thenetworkinglab/difnif/verilog/difnif_top.v

// DifNif
//
// Copyright (c) 2021 Eric Schlaepfer
// This work is licensed under CERN-OHL-S-2.0.
//
`default_nettype none
module difnif_top(
    // Clocks
    input clk_10m,

    // Unknown, FIXME better name
    input chreset_l,

    // Bus reset
    input chreset,

    // Micro Channel bus
    input cmd_l,        // Command clock
    input s0_w_l,       // S0 aka write#
    input s1_r_l,       // S1 aka read#
    input m_io_l,       // memory / IO# transfer
    input cd_setup_l,   // Card setup mode
    input addr_sel_in_l,// Card address selected
    input [15:0] bus_a, // Address bus (register select)
    input fulladdr_l,   // When high, only use 4 bits of address
    input sbhe_l,       // With bus_a0, selects 8 or 16 bit transfer
    output cd_ds16_l,   // Assert low to request 16-bit transfer
    output cd_chrdy_l,  // Channel ready (inserts wait states)
    output cd_sfdbk_l,  // Card selected feedback (72-pin only)

    inout[15:0]bus_d,   // Bidirectional data bus
    output data_dir,    // Data bus buffer direction control

    output irq14_l,     // Interrupt line

    input arb_gnt_l,    // DMA arbitration/grant mode
    input tc_l,         // DMA terminate count
    input [3:0]arb,     // DMA arbitration bus inputs
    input burst_l,      // DMA burst request input
    input preempt_l,    // DMA preempt request input
    output [3:0]arb_o,  // DMA arbitration control line outputs
    output burst_o_l,   // DMA burst request output
    output preempt_o_l, // DMA preempt request output

    // SD card (temporarily used for testing)
    output sd_clk,
    output sd_cmd,
    output [3:0]sd_d,
    input sd_switch,

    // LEDs
    output led0,
    output led1,

    // Teensy
    input tn_rd,
    input tn_wr,
    input [3:0]tn_addr,
    inout [15:0]tn_d,
    output tn_int,
    output tn_clk,
    input tn30
    );

    reg[22:0] counter;
    wire pll_lock;
    wire clk;

    // Teensy registers and controls
    wire [7:0] t_atn;
    wire t_atn_full;
    wire t_atn_read;
    wire [7:0] t_isr_out;
    wire t_isr_full;
    wire t_isr_write;
    wire [15:0] t_cifr;
    wire t_cifr_full;
    wire t_cifr_read;
    wire [15:0] t_sifr_out;
    wire t_sifr_full;
    wire t_sifr_write;

    wire [15:0] t_dreg_out;
    wire [15:0] t_dreg_in;
    wire t_treq_set;
    wire t_treq;
    wire t_treq_16;

    wire t_hard_reset;
    wire t_cmd_in_progress;
    wire t_busy_clear;
    wire t_clear_all;

    wire [39:0] t_pos_regs;

    wire addr_sel_l;
    wire fulladdr2_l;

    // Use pullup on fulladdr_l signal.
    SB_IO #(
        .PIN_TYPE(6'b0000_01),
        .PULLUP(1'b1)
    ) fulladdr_pad (
        .PACKAGE_PIN(fulladdr_l),
        .D_IN_0(fulladdr2_l)
    );

    // Address decoder for 72-pin version: 3510-3517, or 3518-351F when
    // POS 2 bit 1 selects the alternate address. The ThinkPad's system board
    // decodes the address itself and supplies addr_sel_in_l.
    wire alt_addr = t_pos_regs[17];
    assign addr_sel_l = fulladdr2_l ? addr_sel_in_l : ~(bus_a[15:3] == {12'h351, alt_addr});
    wire [3:0] reg_sel = fulladdr2_l ? bus_a[3:0] : {1'b0, bus_a[2:0]};

    mcabus mca1 (
        .clk(clk),
        .chreset(chreset),
        .chreset_l(chreset_l),
        .cmd_l(cmd_l),
        .s0_w_l(s0_w_l),
        .s1_r_l(s1_r_l),
        .m_io_l(m_io_l),
        .cd_setup_l(cd_setup_l),
        .addr_sel_l(addr_sel_l),
        .bus_a(reg_sel),
        .sbhe_l(sbhe_l),
        .cd_ds16_l(cd_ds16_l),
        .cd_chrdy_l(cd_chrdy_l),
        .cd_sfdbk_l(cd_sfdbk_l),

        .bus_d(bus_d),
        .data_dir(data_dir),

        .irq14_l(irq14_l),

        .arb_gnt_l(arb_gnt_l),
        .tc_l(tc_l),
        .arb(arb),
        .burst_l(burst_l),
        .preempt_l(preempt_l),
        .arb_o(arb_o),
        .burst_o_l(burst_o_l),
        .preempt_o_l(preempt_o_l),
        .test1(sd_clk), // FIXME testing
        .test2(sd_cmd),
        .tbus(sd_d), // more testing

        // Teensy connections
        .t_atn(t_atn),
        .t_atn_full(t_atn_full),
        .t_atn_read(t_atn_read),
        .t_isr_out(t_isr_out),
        .t_isr_full(t_isr_full),
        .t_isr_write(t_isr_write),
        .t_cifr(t_cifr),
        .t_cifr_full(t_cifr_full),
        .t_cifr_read(t_cifr_read),
        .t_sifr_out(t_sifr_out),
        .t_sifr_full(t_sifr_full),
        .t_sifr_write(t_sifr_write),
        .t_hard_reset(t_hard_reset),
        .t_cmd_in_progress(t_cmd_in_progress),
        .t_busy_clear(t_busy_clear),
        .t_dreg_out(t_dreg_out),
        .t_dreg_in(t_dreg_in),
        .t_treq_set(t_treq_set),
        .t_treq(t_treq),
        .t_treq_16(t_treq_16),
        .t_clear_all(t_clear_all),

        .t_pos_regs(t_pos_regs)
    );

    teensy tn1 (
        .tn_rd(tn_rd),
        .tn_wr(tn_wr),
        .tn_addr(tn_addr),
        .tn_d(tn_d),
        .tn_int(tn_int),
        .clk(clk),
        .tn30(tn30),

        // Register interface
        .t_atn(t_atn),
        .t_atn_full(t_atn_full),
        .t_atn_read(t_atn_read),
        .t_isr_out(t_isr_out),
        .t_isr_full(t_isr_full),
        .t_isr_write(t_isr_write),
        .t_cifr(t_cifr),
        .t_cifr_full(t_cifr_full),
        .t_cifr_read(t_cifr_read),
        .t_sifr_out(t_sifr_out),
        .t_sifr_full(t_sifr_full),
        .t_sifr_write(t_sifr_write),
        .t_hard_reset(t_hard_reset),
        .t_cmd_in_progress(t_cmd_in_progress),
        .t_busy_clear(t_busy_clear),
        .t_dreg_out(t_dreg_out),
        .t_dreg_in(t_dreg_in),
        .t_treq_set(t_treq_set),
        .t_treq(t_treq),
        .t_treq_16(t_treq_16),
        .t_clear_all(t_clear_all),

        .t_pos_regs(t_pos_regs)
    );
    // 50MHz
    `ifdef SYNTHESIS
    SB_PLL40_PAD #(
        .FEEDBACK_PATH("SIMPLE"),
        .DIVR(0),
        .DIVF(79),
        .DIVQ(4),
        .FILTER_RANGE(1)
    ) icetest_pll (
        .LOCK(pll_lock),
        .RESETB(1'b1),
        .BYPASS(1'b0),
        .PACKAGEPIN(clk_10m),
        .PLLOUTGLOBAL(clk)
    );
    `else
    assign clk = clk_10m;
    `endif

    assign tn_clk = 1'b0; // No clock for now
    //assign tn_clk = clk; // Clock to Teensy in case I want to make a synchronous interface

//    assign led0 = counter[22];
    assign led0 = fulladdr2_l;
    assign led1 = counter[21];

    always @ (posedge clk)
    begin
        counter <= counter + 1;
    end

endmodule
