thenetworkinglab/difnif/verilog/teensy.v

// DifNif
//
// Copyright (c) 2021 Eric Schlaepfer
// This work is licensed under CERN-OHL-S-2.0.
//

`default_nettype none
module teensy(
    // External connections to Teensy
    input tn_rd,
    input tn_wr,
    input [3:0]tn_addr,
    inout [15:0]tn_d,
    output tn_int,
    input clk,
    input tn30,

    // Connections to MCA interface
    // ATN register
    input [7:0] t_atn,
    input t_atn_full,
    output t_atn_read,

    // ISR register
    output [7:0] t_isr_out,
    input t_isr_full,
    output t_isr_write,

    // CIFR register
    input [15:0] t_cifr,
    input t_cifr_full,
    output t_cifr_read,

    // SIFR register
    output [15:0] t_sifr_out,
    input t_sifr_full,
    output t_sifr_write,

    // Flags
    input t_hard_reset,
    output t_cmd_in_progress,
    output t_busy_clear,
    output t_clear_all,

    // Data register
    input [15:0] t_dreg_out,
    output [15:0] t_dreg_in,
    output t_treq_set,
    input t_treq,
    input t_treq_16,

    input [39:0] t_pos_regs
    );

    localparam REG_TEST = 4'd0;
    localparam REG_FLAGS = 4'd1;
    localparam REG_ATN = 4'd2;
    localparam REG_ISR = 4'd3;
    localparam REG_CIFR = 4'd4;
    localparam REG_SIFR = 4'd5;
    localparam REG_DREG = 4'd6;
    localparam REG_POS01 = 4'd7;
    localparam REG_POS23 = 4'd8;
    localparam REG_POS4 = 4'd9;

    reg [15:0] tn_d_out;

    wire [15:0] flags_out;
    reg [15:0] flags_in = 16'H0000;

    reg [15:0] testreg = 16'HABCD;

    reg [7:0] t_isr;
    reg [15:0] t_sifr;
    reg [15:0] t_dreg;

    assign t_isr_out = t_isr;
    assign t_sifr_out = t_sifr;
    assign t_dreg_in = t_dreg;

    // Interrupt output
    assign tn_int = t_atn_full; // TODO: make this more complex

    wire t_busy_bit;

    // Flag register
    assign flags_out = {5'h0, t_clear_all,
                        t_treq_16, t_treq,
                        1'b1, t_cmd_in_progress, // Clear busy is active low
                        1'b0, t_hard_reset,
                        t_sifr_full, t_cifr_full,
                        t_isr_full, t_atn_full};

    // These bits in the flag reg are r/w
    assign t_cmd_in_progress = flags_in[6];
    assign t_clear_all = flags_in[10]; // ATN, BUSY, CI FULL, ISR, SI FULL, TREQ, TREQ_16
    // Note: Does not clear CmdInProgress

    // Clears the busy flag when bit is written to a '0'
    assign t_busy_clear = tn_wr & (tn_addr == REG_FLAGS) & ~tn_d[7];

    // Sets the transfer request flag when bit is written to a '1'
    assign t_treq_set = tn_wr & (tn_addr == REG_FLAGS) & tn_d[5];

    // Data outputs
    assign tn_d = tn_rd ? tn_d_out : 16'bZ;
    always @ (*) begin
        case (tn_addr)
            REG_TEST   : tn_d_out <= testreg;
            REG_FLAGS  : tn_d_out <= flags_out;
            REG_ATN    : tn_d_out <= {8'H0, t_atn};
            REG_ISR    : tn_d_out <= {8'H0, t_isr};
            REG_SIFR   : tn_d_out <= t_sifr;
            REG_CIFR   : tn_d_out <= t_cifr;
            REG_DREG   : tn_d_out <= t_dreg_out;
            REG_POS01  : tn_d_out <= t_pos_regs[15:0];
            REG_POS23  : tn_d_out <= t_pos_regs[31:16];
            REG_POS4   : tn_d_out <= t_pos_regs[39:32];
            default    : tn_d_out <= 16'H0;
        endcase
    end

    // Capture data on rising edge of tn_wr
    always @ (posedge tn_wr) begin
        case (tn_addr)
            REG_TEST   : testreg <= tn_d;
            REG_FLAGS  : flags_in <= tn_d;
            REG_ISR    : t_isr <= tn_d;
            REG_SIFR   : t_sifr <= tn_d;
            REG_DREG   : t_dreg <= tn_d;
        endcase
    end

    // Used to set/clear handshaking flags
    assign t_atn_read = tn_rd & (tn_addr == REG_ATN);
    assign t_isr_write = tn_wr & (tn_addr == REG_ISR);
    assign t_cifr_read = tn_rd & (tn_addr == REG_CIFR);
    assign t_sifr_write = tn_wr & (tn_addr == REG_SIFR);

endmodule
